famicomical/PIC-nixie/docs/nixie related/Burroughs-Cat-616.pdf

www.tube-tester.com

File created by Dieter Waechter

# Dieter’s Nixie Tube Data Archive

This file is a part of Dieter's Nixie- and display tubes data archive

If you have more datasheets, articles, books, pictures or other information about Nixie tubes or other display devices please let me know. Thank you!

Document in this file | Burroughs Catalogue 616 (Nixie Indicator Tubes - Characteristics and Circuit Design Data) Dated approx. 1962
Display devices in this document | 6844A, 7009, 7009L, 7153, 7977, 7977L, 8037, B4021, B4021L, B4022, B4028, B4031, B4032, B4081, B4081L, B50113, B5016, B5018, B5031, B5032, B50911, B5092, B5094, B6012, B6033, B6034, B6037, B6091, B7094, B8091, BD-214, BD-216, BD-221, BD-255, BX1000, BX2000, BX-2001, SK106, SK109, SK112, SK116A, SK118A, SK119A, SK120, SK124, SK125, SK127, SK128
