famicomical/PIC-nixie/docs/nixie related/Bally Nixie MUX example.pdf

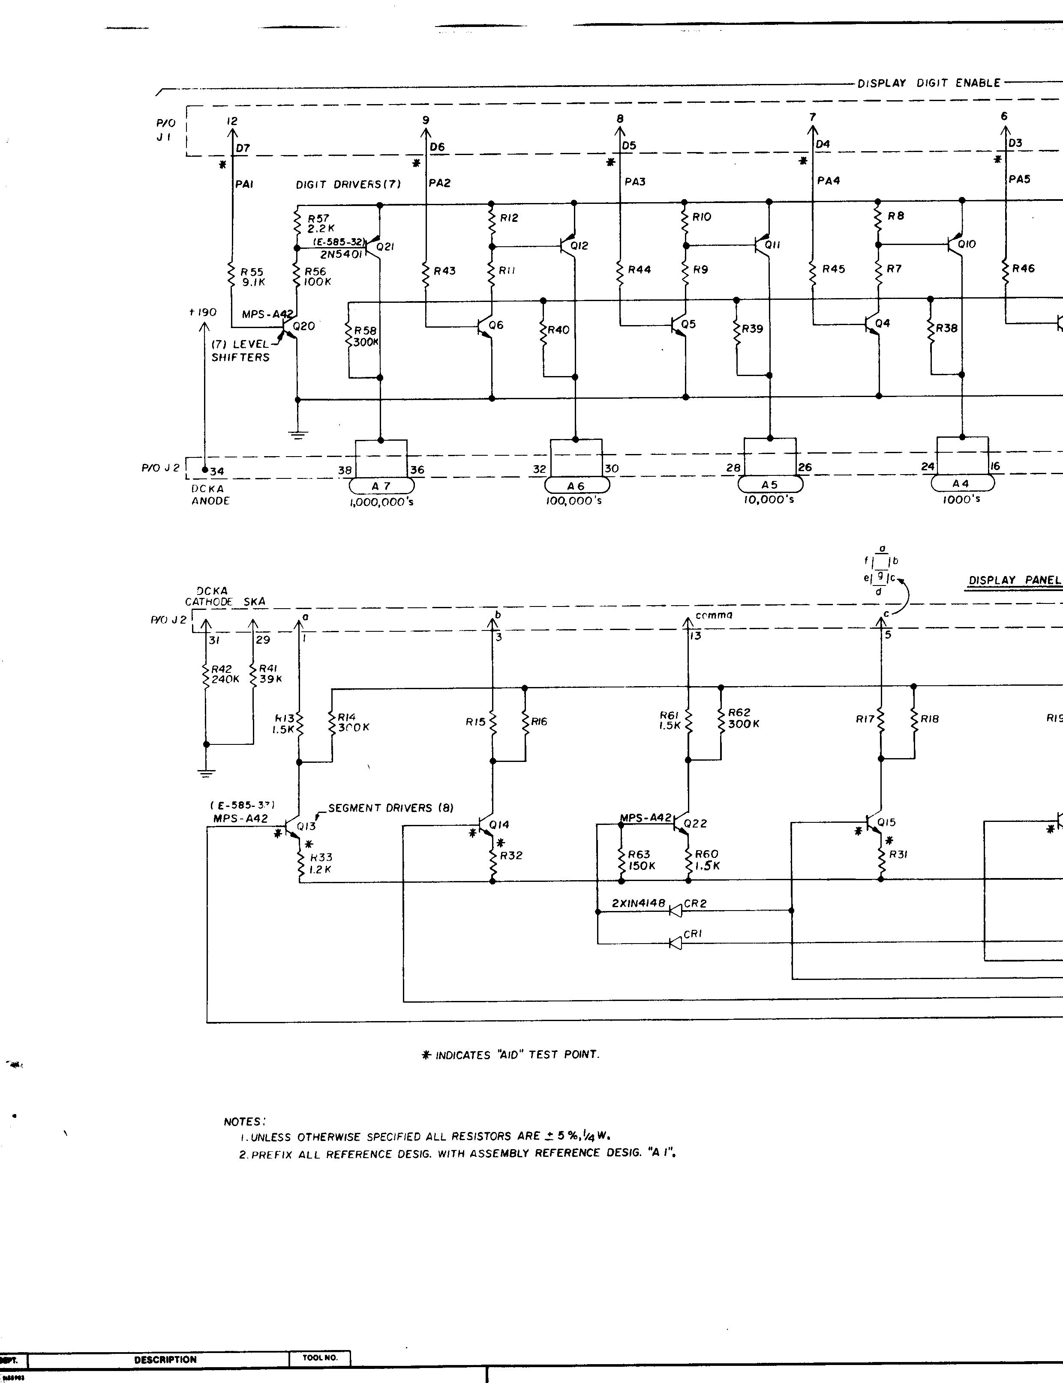
[picture p5: page 1]
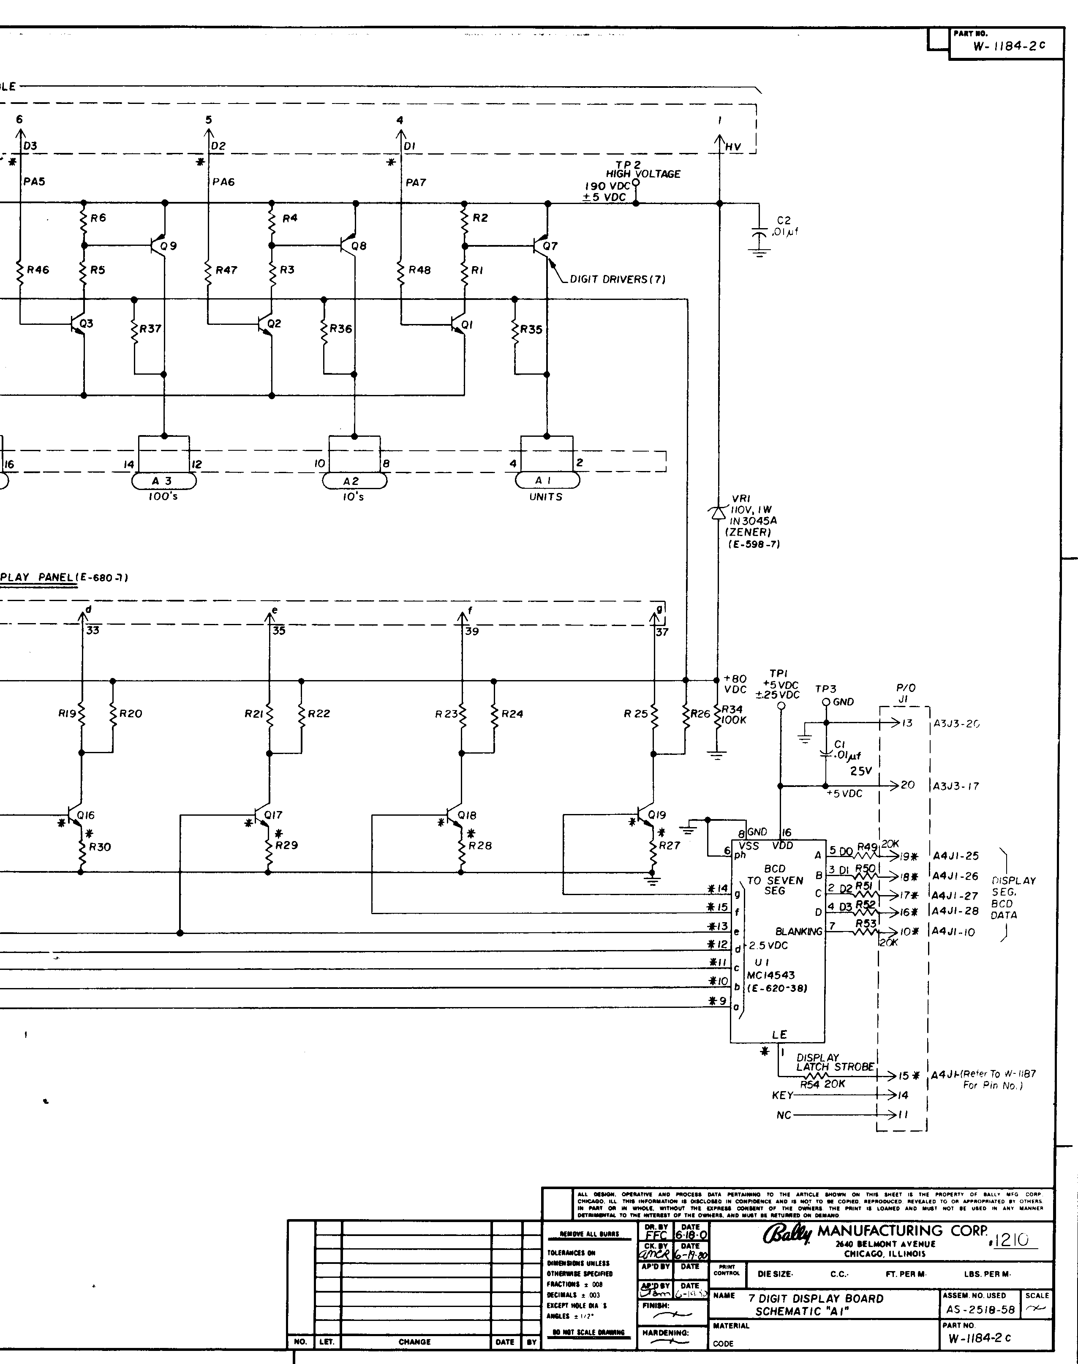
[picture p6: page 2]
