famicomical/PIC-nixie/simulations/colon.asc

A1: inv; td=50n Vhigh=5
A2: inv; td=10n Vhigh=5
Q1: npn; PMBTA42
Q2: npn; PMBTA42
R1: res; 2.2k
R2: res; 120k
R3: res; 120k
U2: neonbulb; Vstrike=90 Vhold=60; Zon=2K Ihold=700u
V1: voltage; PULSE(0 5 1m 10n 10n 1m 2m 4)
V2: voltage; 170
Named nets: 0
.op
.tran 0 8m 1n
