famicomical/PIC-nixie/simulations/nixie.asc

C1: cap; 2.2µ
D1: zener; BZX384B68
D2: zener; BZX384B68
M1: pmos; BSR92P_L0
Q1: npn; PMBTA42
Q2: npn; PMBTA42
R1: res; 5.1k
R2: res; 10k
R3: res; 8.2k
R4: res; 220k
R5: res; 1k
R6: res; 220k
R7: res; 1Meg
R8: res; 20m
U1: neonbulb; Vstrike=160 Vhold=140; Zon=2K Ihold=2m
V1: voltage; 170
V2: voltage; PULSE(0 5 0.1m 1n 1n 0.5m 1m 3)
V3: voltage; PULSE(0 5 0.2m 1n 1n 1m 2m 2)
Named nets: 0
.op
.include PMBTA42.TXT
.tran 4m
.lib Pchannel_250V.lib
.temp 25
